ruoso/feather-smart-thermostat/_saved_feather-smart-thermostat.sch

## KiCad design _saved_feather-smart-thermostat.sch (2020-10-16)

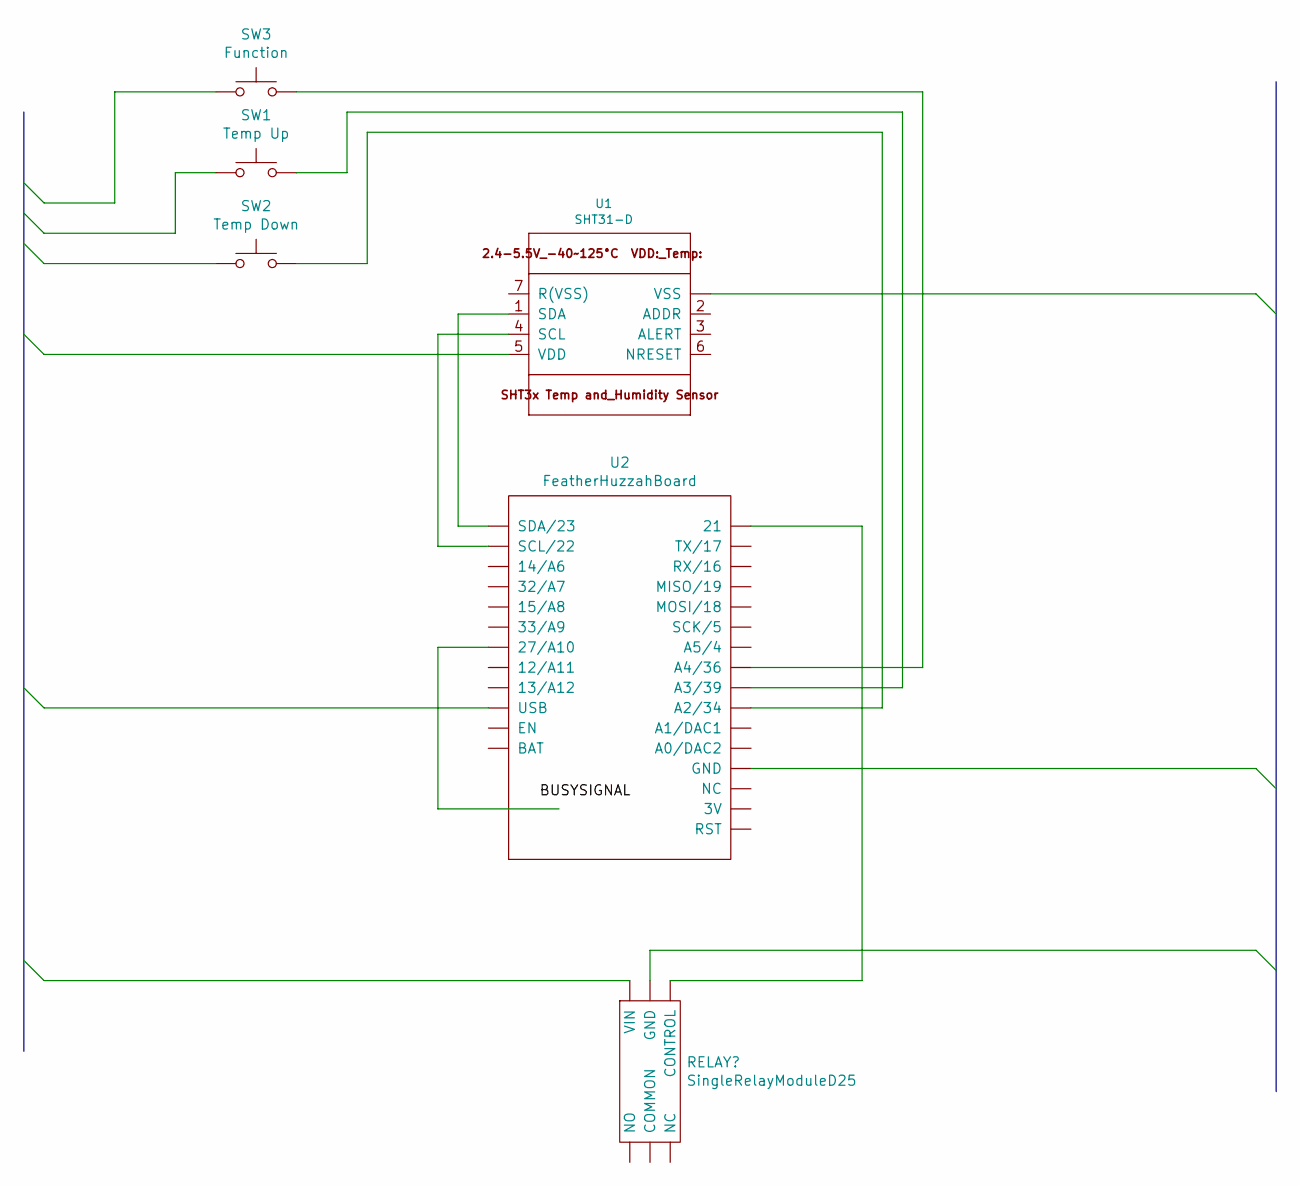
[picture p4: schematic _saved_feather-smart-thermostat.sch]

Parts:
SW1: Temp Up
SW2: Temp Down
SW3: Function
U1: SHT31-D
U2: FeatherHuzzahBoard

Connections:
unnamed: SW1.2, U2.~
unnamed: SW2.2, U2.~
unnamed: SW3.2, U2.~
unnamed: U1.1 (SDA), U2.~
unnamed: U1.4 (SCL), U2.~
unnamed: U1.8 (VSS), U1.THERMAL (VSS)
